j5bot/proton-pack-wiring/amp-audio/amp.png

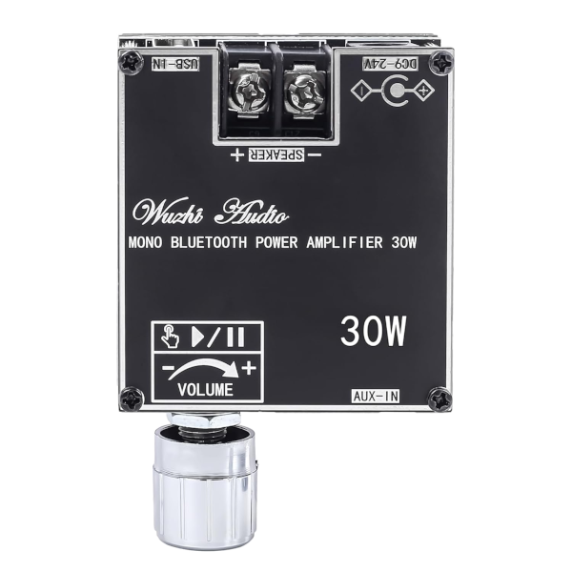
amp-audio/amp.png
