j5bot/proton-pack-wiring/panel/graphics/panel design.png

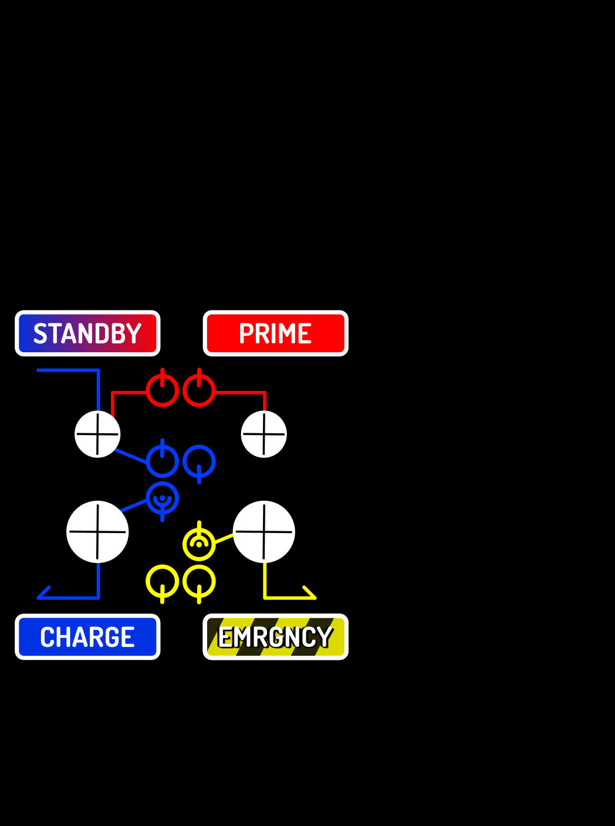
panel/graphics/panel design.png
