j5bot/proton-pack-wiring/panel/photos/battery compartment notch.jpg

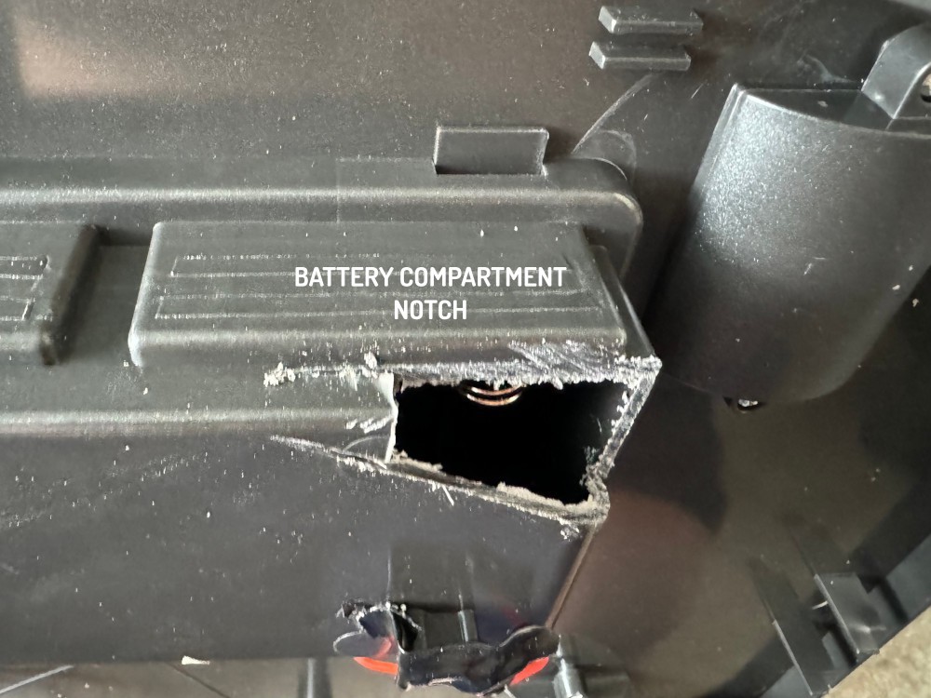
panel/photos/battery compartment notch.jpg
