j5bot/proton-pack-wiring/panel/photos/booster tube cavity-sm.jpg

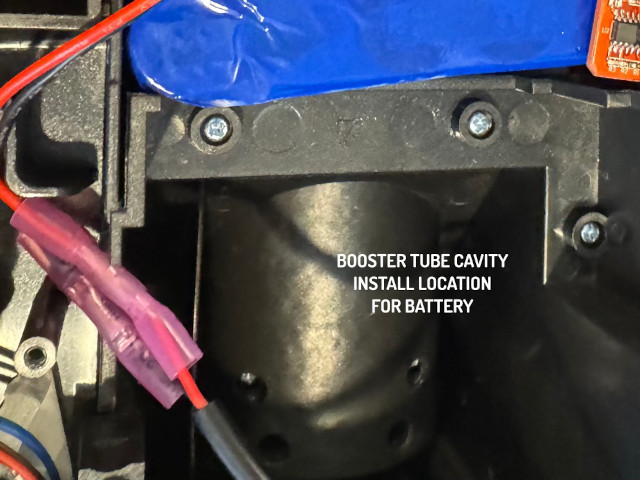
panel/photos/booster tube cavity-sm.jpg
