j5bot/proton-pack-wiring/panel/photos/corner notch.jpg

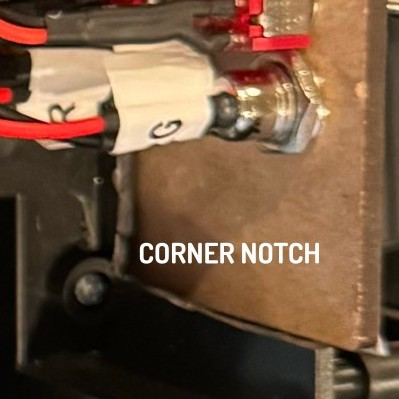
panel/photos/corner notch.jpg
