j5bot/proton-pack-wiring/panel/photos/panel - pack open.jpg

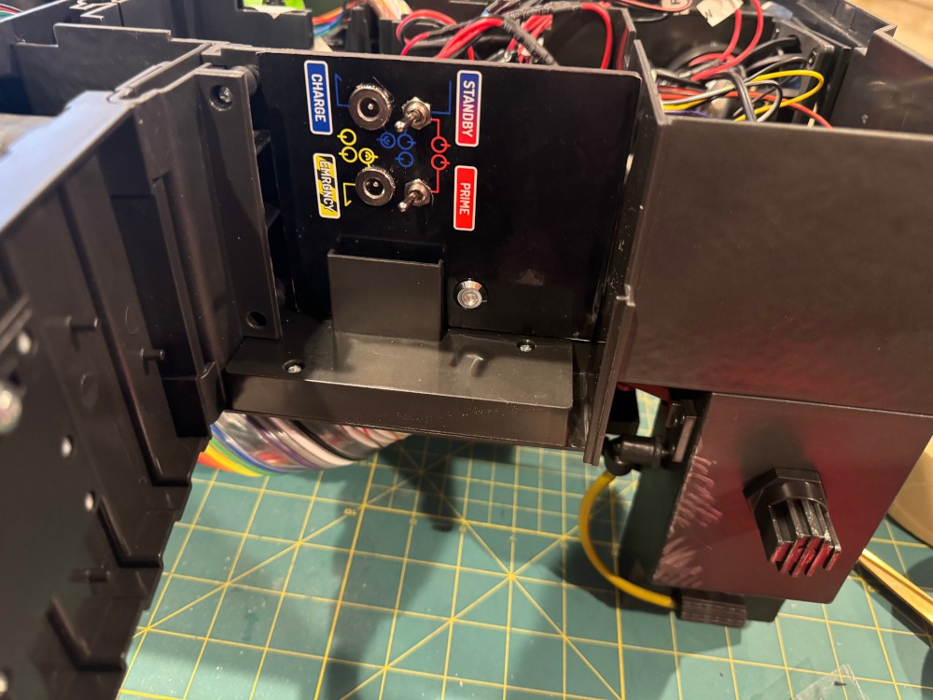
panel/photos/panel - pack open.jpg
