j5bot/proton-pack-wiring/panel/photos/talentcell circuit board location.jpg

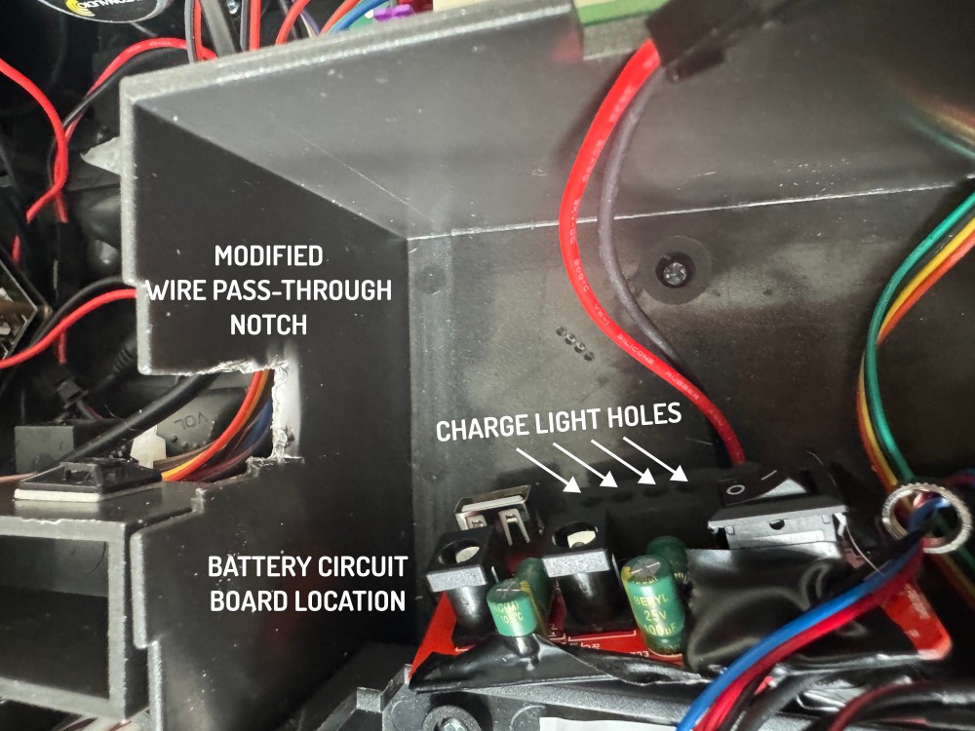
panel/photos/talentcell circuit board location.jpg
