j5bot/proton-pack-wiring/panel/photos/talentcell in booster tube cavity-sm.jpg

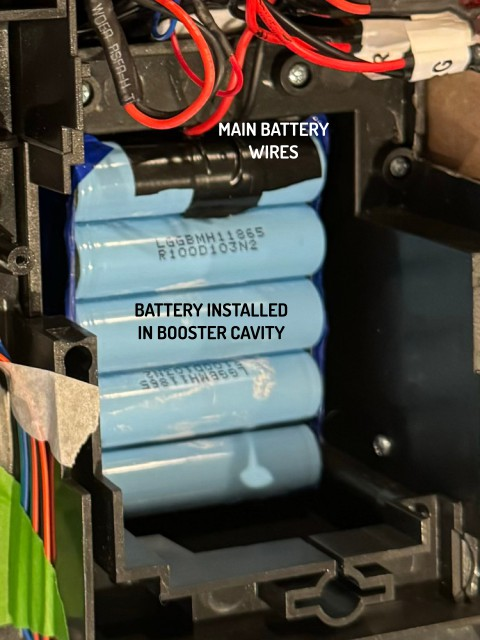
panel/photos/talentcell in booster tube cavity-sm.jpg
