j5bot/proton-pack-wiring/panel/photos/original wiring location-sm.jpg

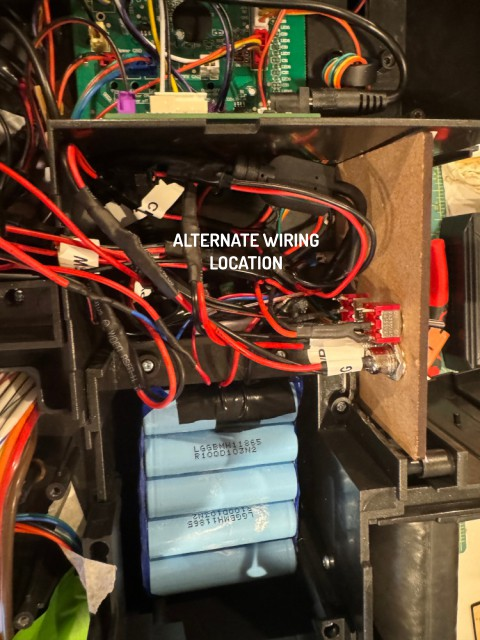
panel/photos/original wiring location-sm.jpg
