j5bot/proton-pack-wiring/panel/photos/wiring positions-sub.jpg

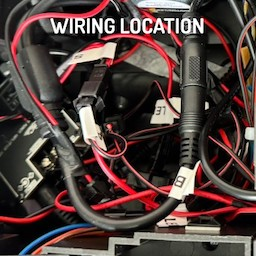
panel/photos/wiring positions-sub.jpg
